keerthana681/Cat-Ninja-Project/software/LED.h

/*
 * LED.h
 *
 *  Created on: Nov 5, 2023
 *      Author:
 */

#ifndef LED_H_
#define LED_H_
#include <stdint.h>

// initialize your LEDs
void LED_Init(void);

void LED_SetLives(uint8_t lives); // 0-3, lights up that many LEDs

// data specifies which LED to turn on
void LED_On(uint32_t data);

// data specifies which LED to turn off
void LED_Off(uint32_t data);

// data specifies which LED to toggle
void LED_Toggle(uint32_t data);


#endif /* LED_H_ */
